Aryan-git-byte/CIPHER/Docs/images/Schematic/Schematic_page-0003.jpg

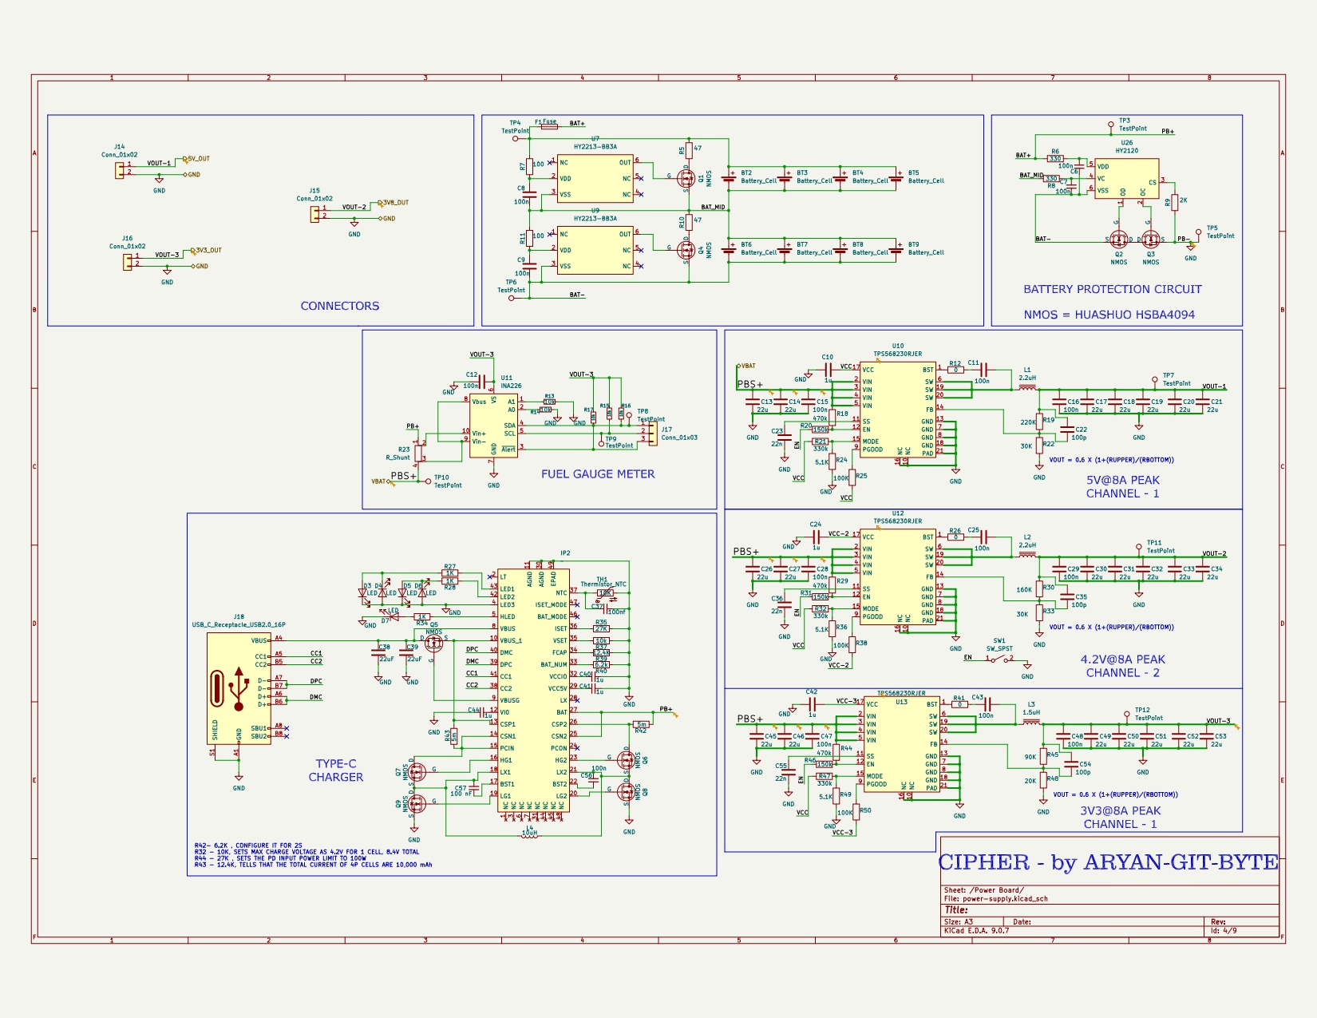
Docs/images/Schematic/Schematic_page-0003.jpg
