Aryan-git-byte/CIPHER/kicad/Lattepanda/carrier/carrier.kicad_pcb

## KiCad design kicad/FM-ANS_LC-VCO-V3/FM-ELK.kicad_pcb

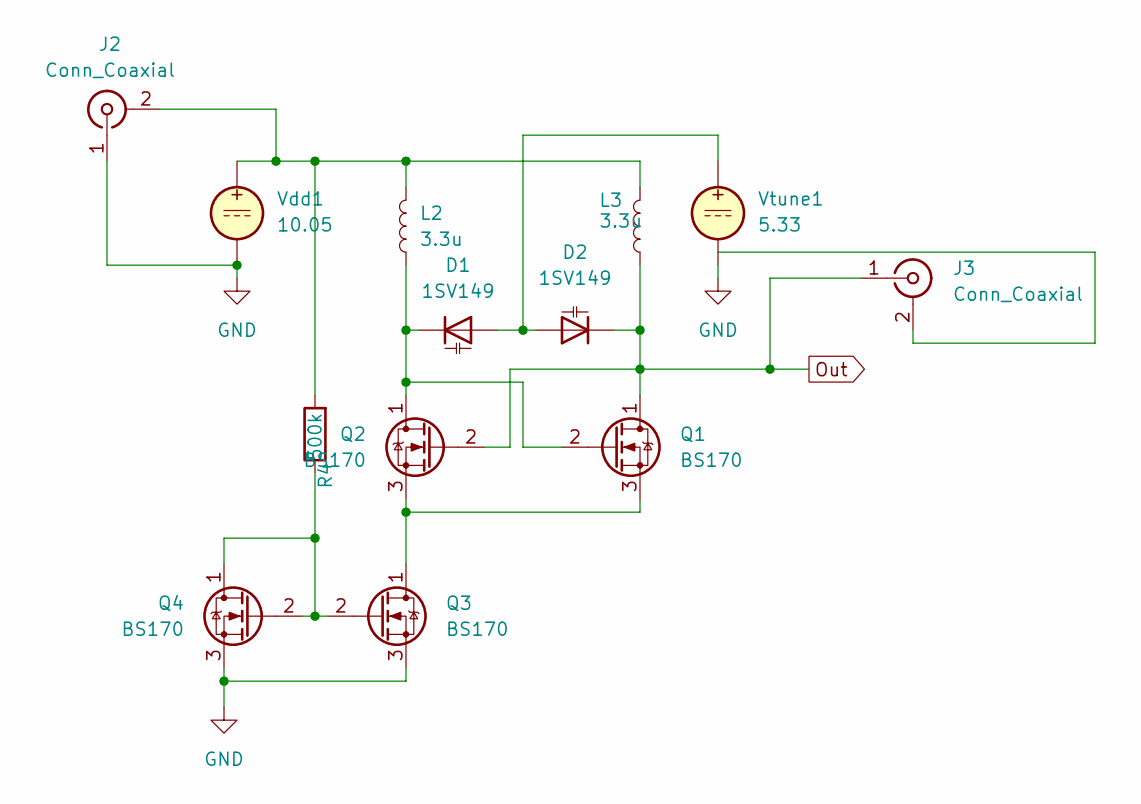
[picture p60: schematic FM-ELK.kicad_sch, Name of circuit / Creator]

Parts:
D1, D2: 1SV149; TO-92_Inline
J2, J3: Conn_Coaxial; BNC_Amphenol_031-5539_Vertical
L2, L3: 3.3u; L_Radial_D10.0mm_P5.00mm_Fastron_07P
Q1, Q2, Q3, Q4: BS170; TO-92_Inline
R4: 500k; R_Axial_DIN0207_L6.3mm_D2.5mm_P7.62mm_Horizontal
Vdd1: 10.05; PinHeader_1x02_P2.54mm_Vertical
Vtune1: 5.33; PinHeader_1x02_P2.54mm_Vertical

Connections:
GND: J2.1 (In), Q3.3 (S), Q4.3 (S), Vdd1.2, Vtune1.2
unnamed: D1.2 (A), D2.2 (A), Vtune1.1
unnamed: D1.1 (K), L2.1, Q1.2 (G), Q2.1 (D)
unnamed: J2.2 (Ext), L2.2, L3.2, R4.2, Vdd1.1
unnamed: Q1.3 (S), Q2.3 (S), Q3.1 (D)
unnamed: Q3.2 (G), Q4.1 (D), Q4.2 (G), R4.1
Out: D2.1 (K), J3.1 (In_1), L3.1, Q1.1 (D), Q2.2 (G)

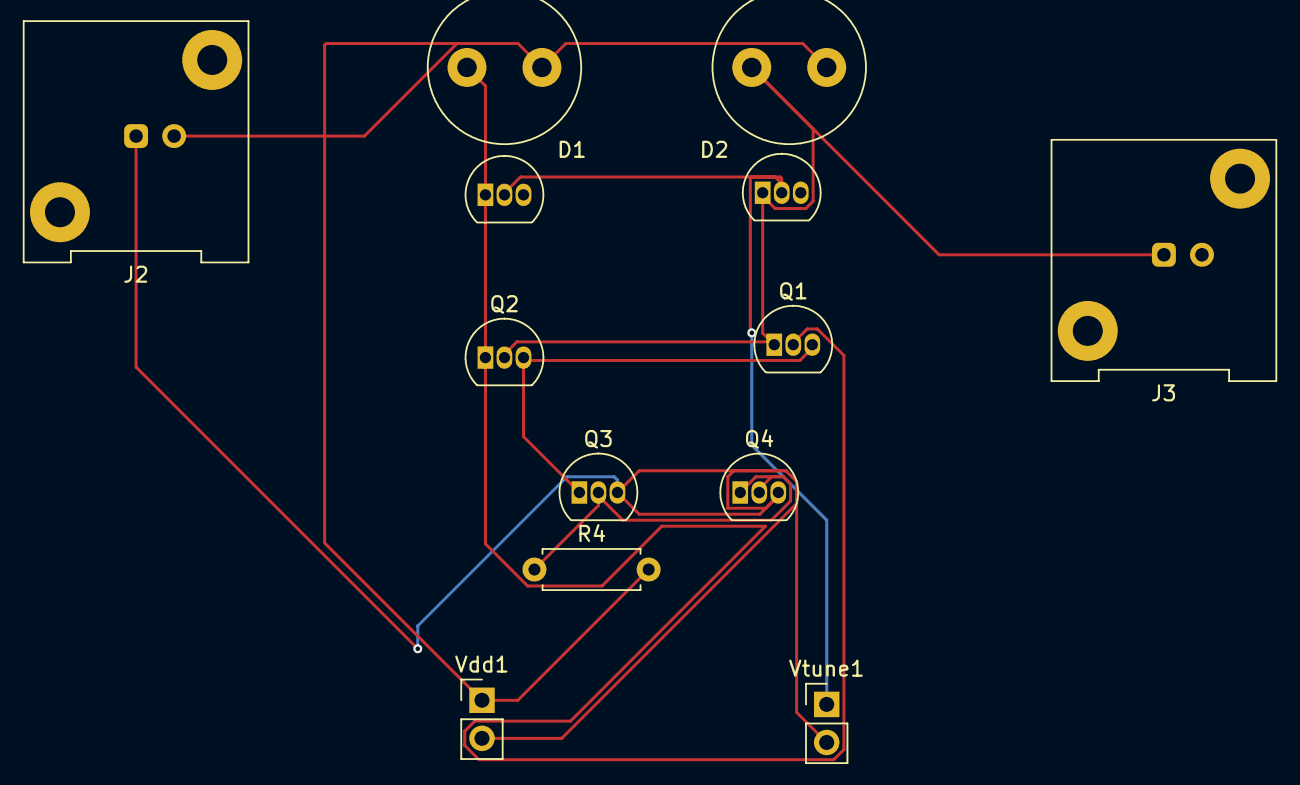
[picture p61: board FM-ELK.kicad_pcb from above]

Board: 2 copper layers, 13 parts (0 on the bottom side), 7 nets.
