Aryan-git-byte/CIPHER/kicad/Lattepanda/carrier/carrier.kicad_pcb

## KiCad design kicad/FM-VCO/FM-VCO.kicad_pcb

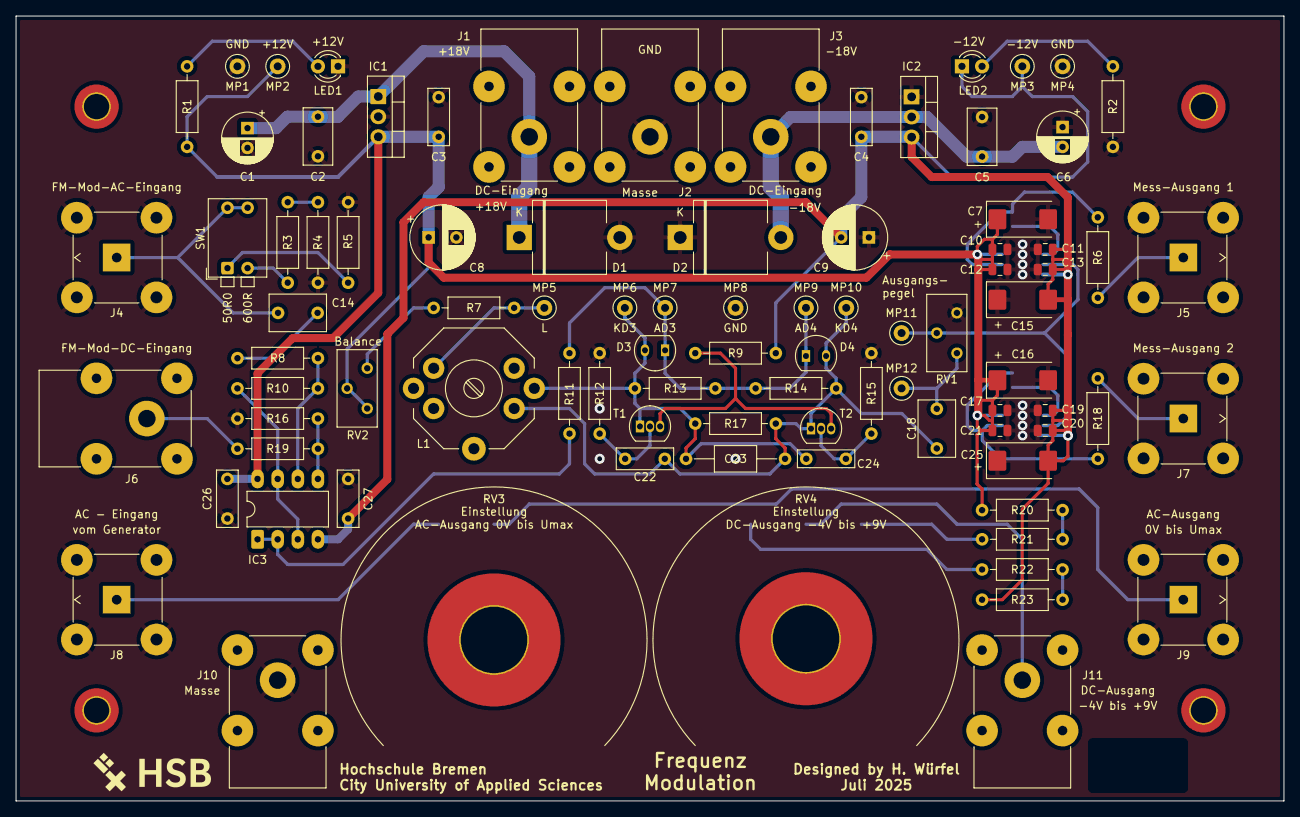
[picture p62: board FM-VCO.kicad_pcb from above]

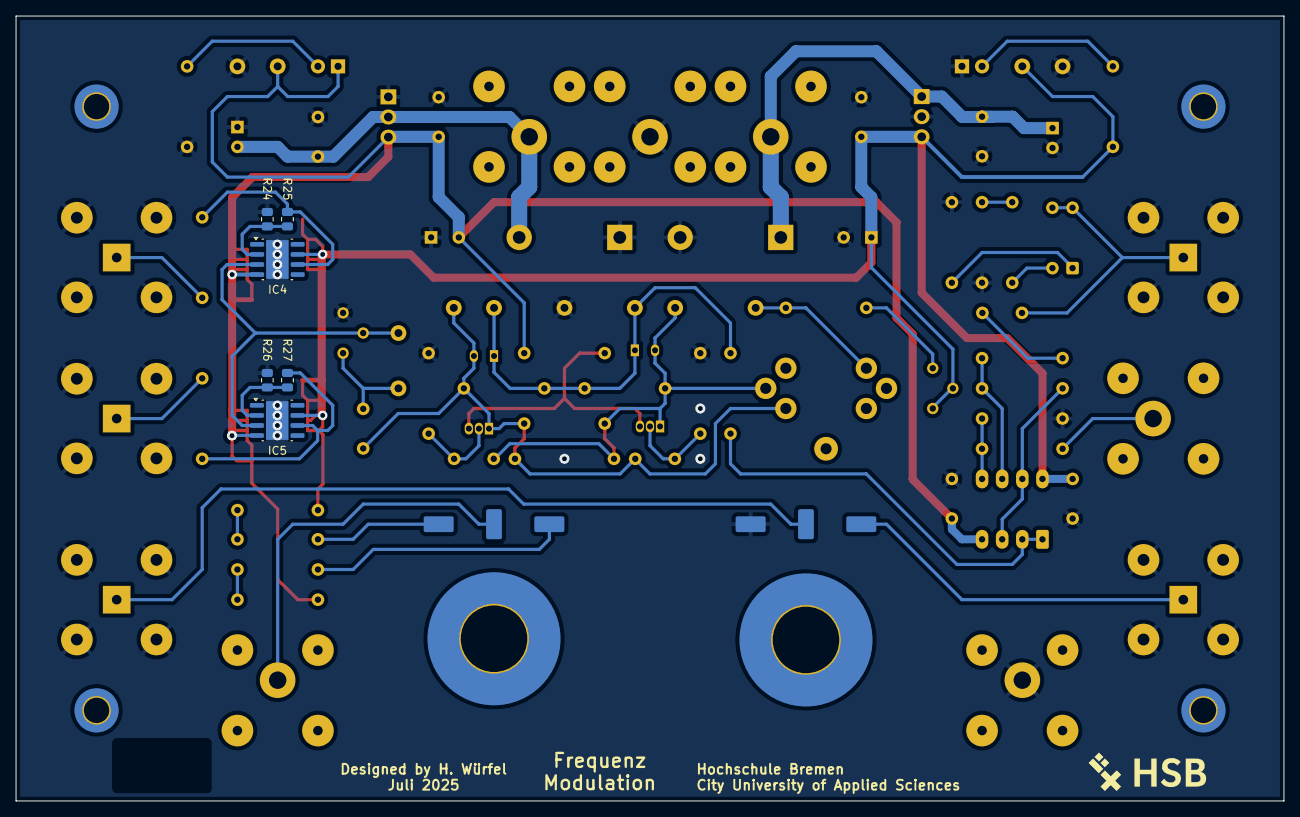
[picture p63: board FM-VCO.kicad_pcb from below]

Board: 2 copper layers, 160.0 x 99.1 mm, 104 parts (7 on the bottom side), 40 nets.

Parts:
C1, C6: 10µ; CP_Radial_D6.3mm_P2.50mm
C2, C5: 330n; C_Rect_L7.0mm_W3.5mm_P5.00mm
C3, C4, C26, C27: 100n; C_Rect_L7.0mm_W2.5mm_P5.00mm
C7, C15, C16, C25: 10µ; CP_EIA-7343-31_Kemet-D_Pad2.25x2.55mm_HandSolder
C8, C9: 100µ; CP_Radial_D8.0mm_P3.50mm
C10, C13, C17, C20: 1n; C_0805_2012Metric
C11, C12, C19, C21: 47n; C_0805_2012Metric
C14, C18: 1µ0; C_Rect_L7.0mm_W4.5mm_P5.00mm
C22: 22n; C_Rect_L7.0mm_W2.5mm_P5.00mm
C23: 68p; C_Axial_L5.1mm_D3.1mm_P12.50mm_Horizontal
C24: 22n; C_Rect_L7.0mm_W2.0mm_P5.00mm
D1, D2: P600G; D_P600_R-6_P12.70mm_Horizontal
D3, D4: BB112
G*: LOGO; HSB-Logo
G*#2: LOGO; HSB-Logo
H1, H2, H5, H6: MountingHole; MountingHole_3.2mm_M3_DIN965_Pad_TopBottom
H3, H4: MountingHole; MountingHole_8.4mm_M8_Pad_TopBottom
IC1: LM7812_TO220; TO-220-3_Vertical
IC2: LM7912_TO220; TO-220-3_Vertical
IC3: TL082; DIP-8_W7.62mm_LongPads
IC4, IC5: THS3091DDAR; Texas_R-PDSO-G8_EP2.95x4.9mm_Mask2.4x3.1mm
J1: +18V; Banana_Cliff_FCR7350B_S16N-PC_Horizontal_modi
J2, J10: GND; Banana_Cliff_FCR7350B_S16N-PC_Horizontal_modi
J3: -18V; Banana_Cliff_FCR7350B_S16N-PC_Horizontal_modi
J4: FM-Mod-AC-Eingang; BNC_TEConnectivity_1478035_Horizontal
J5: Mess-Ausgang 1; BNC_TEConnectivity_1478035_Horizontal
J6: FM-Mod-DC-Eingang; Banana_Cliff_FCR7350B_S16N-PC_Horizontal_modi
J7: Mess-Ausgang 2; BNC_TEConnectivity_1478035_Horizontal
J8: AC - Eingang; BNC_TEConnectivity_1478035_Horizontal
J9: AC-Ausgang; BNC_TEConnectivity_1478035_Horizontal
J11: DC-Ausgang; Banana_Cliff_FCR7350B_S16N-PC_Horizontal_modi
L1: 7µ 7µ; Spule_Vielstedter_14mm
LED1, LED2: gn; LED_D3.0mm_Clear
MP1, MP4, MP8: GND; TestPoint_Loop_D2.50mm_Drill1.0mm
MP2: +12V; TestPoint_Loop_D2.50mm_Drill1.0mm
MP3: -12V; TestPoint_Loop_D2.50mm_Drill1.0mm
MP5: L; TestPoint_Loop_D2.50mm_Drill1.0mm
MP6: KD3; TestPoint_Loop_D2.50mm_Drill1.0mm
MP7: AD3; TestPoint_Loop_D2.50mm_Drill1.0mm
MP9: AD4; TestPoint_Loop_D2.50mm_Drill1.0mm
MP10: KD4; TestPoint_Loop_D2.50mm_Drill1.0mm
MP11: U-Treiber-In; TestPoint_Loop_D2.50mm_Drill1.0mm
MP12: Pegel; TestPoint_Loop_D2.50mm_Drill1.0mm
R1, R2: 470R; R_Axial_DIN0207_L6.3mm_D2.5mm_P10.16mm_Horizontal
R3: 590R; R_Axial_DIN0207_L6.3mm_D2.5mm_P10.16mm_Horizontal
R4: 10R0; R_Axial_DIN0207_L6.3mm_D2.5mm_P10.16mm_Horizontal
R5, R6, R18: 50R0; R_Axial_DIN0207_L6.3mm_D2.5mm_P10.16mm_Horizontal
R7: 3K3; R_Axial_DIN0207_L6.3mm_D2.5mm_P10.16mm_Horizontal
R8, R9, R10, R12, R15, R16, R19: 10K0; R_Axial_DIN0207_L6.3mm_D2.5mm_P10.16mm_Horizontal
R11: 4K7; R_Axial_DIN0207_L6.3mm_D2.5mm_P10.16mm_Horizontal
R13, R14: 22K0; R_Axial_DIN0207_L6.3mm_D2.5mm_P10.16mm_Horizontal
R17: 1M0; R_Axial_DIN0207_L6.3mm_D2.5mm_P10.16mm_Horizontal
R20: 1K1; R_Axial_DIN0207_L6.3mm_D2.5mm_P10.16mm_Horizontal
R21: 39R0; R_Axial_DIN0207_L6.3mm_D2.5mm_P10.16mm_Horizontal
R22: 300R; R_Axial_DIN0207_L6.3mm_D2.5mm_P10.16mm_Horizontal
R23: 2K7; R_Axial_DIN0207_L6.3mm_D2.5mm_P10.16mm_Horizontal
R24, R25, R26, R27: 1K2; R_0805_2012Metric
RV1: 20K0; Potentiometer_Bourns_3296Y_Vertical
RV2: 1K0; Potentiometer_Bourns_3296Y_Vertical
RV3: 5K0; Taiss_10Gang_Poti
RV4: 5k0; Taiss_10Gang_Poti
SW1: SW_DIP_x02; SW_DIP_SPSTx02_Piano_CTS_Series194-2MSTN_W7.62mm_P2.54mm
T1, T2: BC546B; TO-92_Inline

Connections:
+12V: C3.1, C7.1, C8.1, C10.1, C12.1, C16.1, C17.2, C21.2, C26.1, IC1.3 (VO), IC3.8 (V+), IC4.7 (V+), IC5.7 (V+), MP2.1, R1.1, R20.2, RV2.1, RV2.2
-12V: C4.2, C9.2, C11.2, C13.2, C15.2, C19.2, C20.2, C25.2, C27.1, IC2.3 (VO), IC3.4 (V-), IC4.4 (V-), IC5.4 (V-), LED2.1 (K), MP3.1, R9.1, R23.2
/FM-Spannungsversorgung/+18V: C1.1, C2.1, D1.1 (K), IC1.1 (VI), J1.1
/FM-Spannungsversorgung/-18V: C5.2, C6.2, D2.2 (A), IC2.2 (VI), J3.1
/IN: IC4.3 (+), IC5.3 (+), MP11.1, RV1.2
/OUT-1: J5.1 (In), R6.2
/OUT-2: J7.1 (In), R18.2
GND: C1.2, C2.2, C3.2, C4.1, C5.1, C6.1, C7.2, C8.2, C9.1, C10.2, C11.1, C12.2, C13.1, C15.1, C16.2, C17.1, C19.1, C20.1, C21.1, C25.1, C26.2, C27.2, D1.2 (A), D2.1 (K), IC1.2 (GND), IC2.1 (GND), IC4.9 (EP), IC5.9 (EP), J2.1, J4.2 (Ext), J5.2 (Ext), J7.2 (Ext), J8.2 (Ext), J9.2 (Ext), J10.1, LED1.1 (K), MP1.1, MP4.1, MP8.1, R2.1, R4.2, R5.2, R12.1, R15.1, R16.2, R24.1, R26.1, RV1.3, RV3.3
unnamed: C14.2, R8.1
unnamed: D3.2 (A), D4.2 (A), MP7.1, MP9.1, R11.1, R13.1, R14.2
unnamed: C23.1, C24.1, D3.1 (K), L1.2, MP6.1, R13.2, R17.1, T1.1 (C)
unnamed: C18.1, C22.2, C23.2, D4.1 (K), L1.3, MP10.1, R14.1, R17.2, T2.1 (C)
unnamed: IC3.3 (+), IC3.7, R10.2
unnamed: IC3.1, IC3.2 (-), R11.2
unnamed: IC3.5 (+), R16.1, R19.2
unnamed: IC3.6 (-), R8.2, R10.1
unnamed: IC4.2 (-), R24.2, R25.1
unnamed: IC4.6, R6.1, R25.2
unnamed: IC5.2 (-), R26.2, R27.1
unnamed: IC5.6, R18.1, R27.2
unnamed: C14.1, J4.1 (In), SW1.3, SW1.4
unnamed: J6.1, R19.1
unnamed: J8.1 (In), RV3.1
unnamed: J9.1 (In), RV3.2
unnamed: J11.1, RV4.2
unnamed: LED1.2 (A), R1.2
unnamed: LED2.2 (A), R2.2
unnamed: L1.6, MP5.1, R7.2
unnamed: C18.2, MP12.1, RV1.1
unnamed: R3.1, SW1.2
unnamed: R3.2, R4.1
unnamed: R5.1, SW1.1
unnamed: R7.1, RV2.3
unnamed: R20.1, R21.2
unnamed: R21.1, RV4.1
unnamed: R22.1, RV4.3
unnamed: R22.2, R23.1
unnamed: C22.1, R12.2, T1.2 (B)
unnamed: R9.2, T1.3 (E), T2.3 (E)
unnamed: C24.2, R15.2, T2.2 (B)
